SepticElectronics/High-Speed-Timer/PrecisionTimer_RevG.1/IO Plate/IO Plate.png

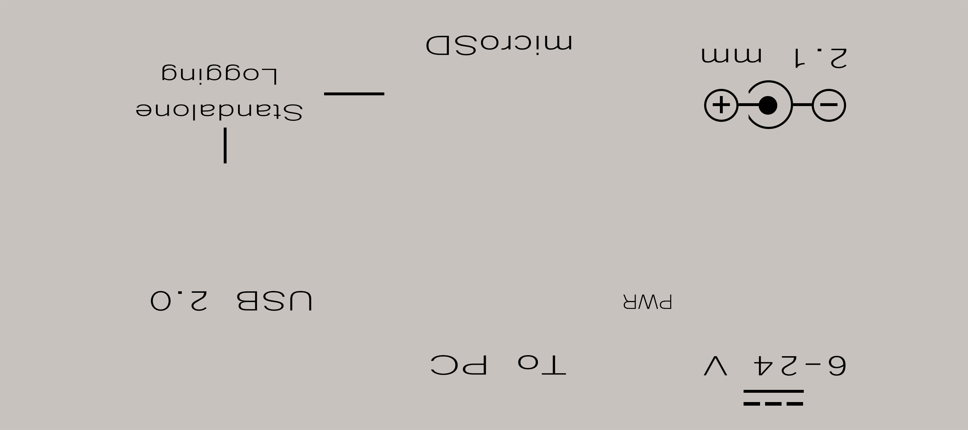
PrecisionTimer_RevG.1/IO Plate/IO Plate.png
