SepticElectronics/High-Speed-Timer/PrecisionTimer_RevG.1/IO Plate/IO Plate_flipped.png

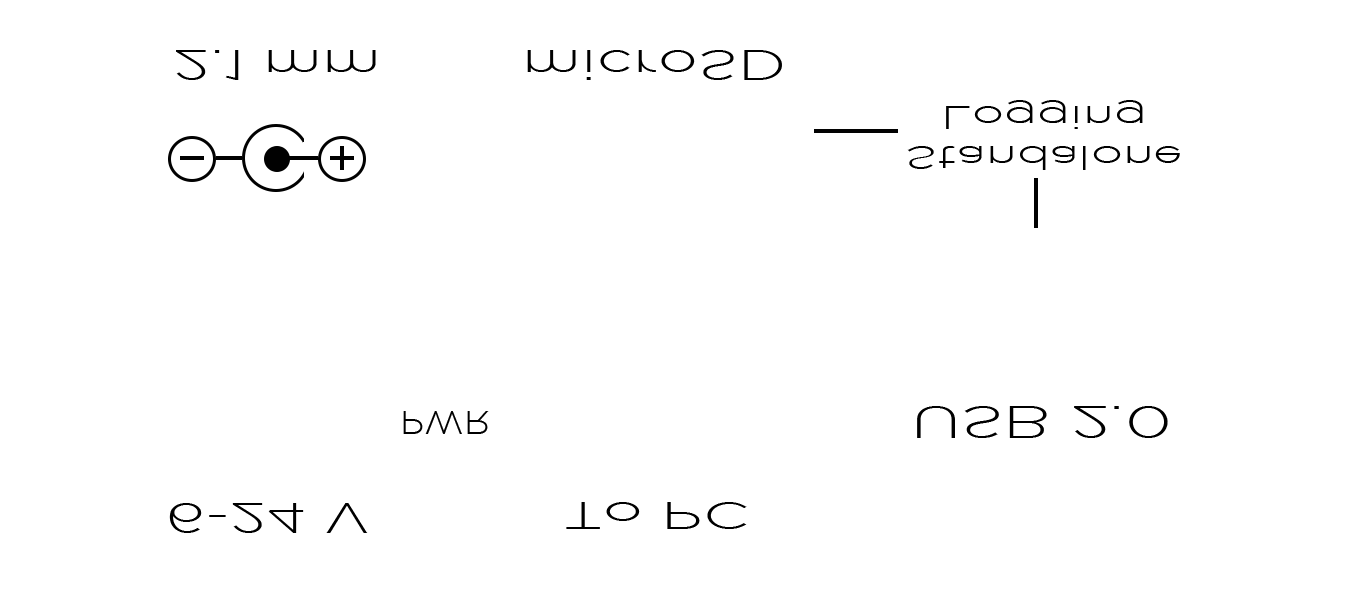
PrecisionTimer_RevG.1/IO Plate/IO Plate_flipped.png
