SepticElectronics/High-Speed-Timer/PrecisionTimer_RevG.1/IO Plate/Trig Plate.png

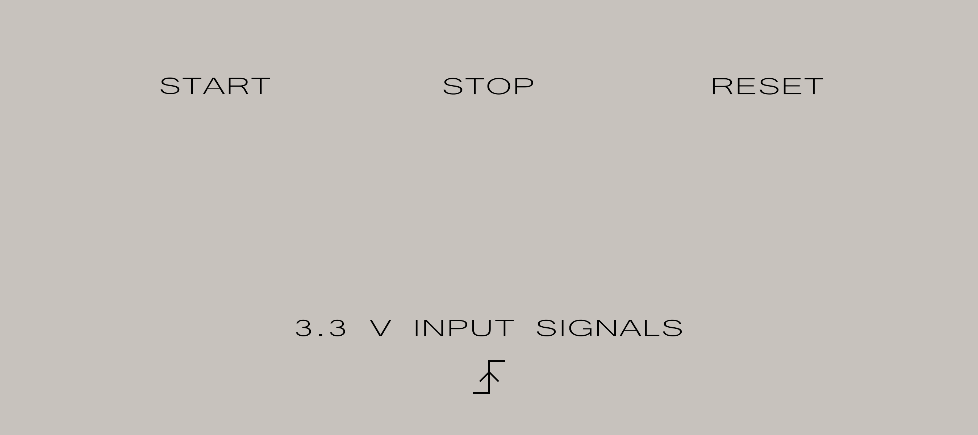
PrecisionTimer_RevG.1/IO Plate/Trig Plate.png
