SepticElectronics/High-Speed-Timer/PrecisionTimer_RevG.1/render/PrecisionTimer_RevG-1_Front2.png

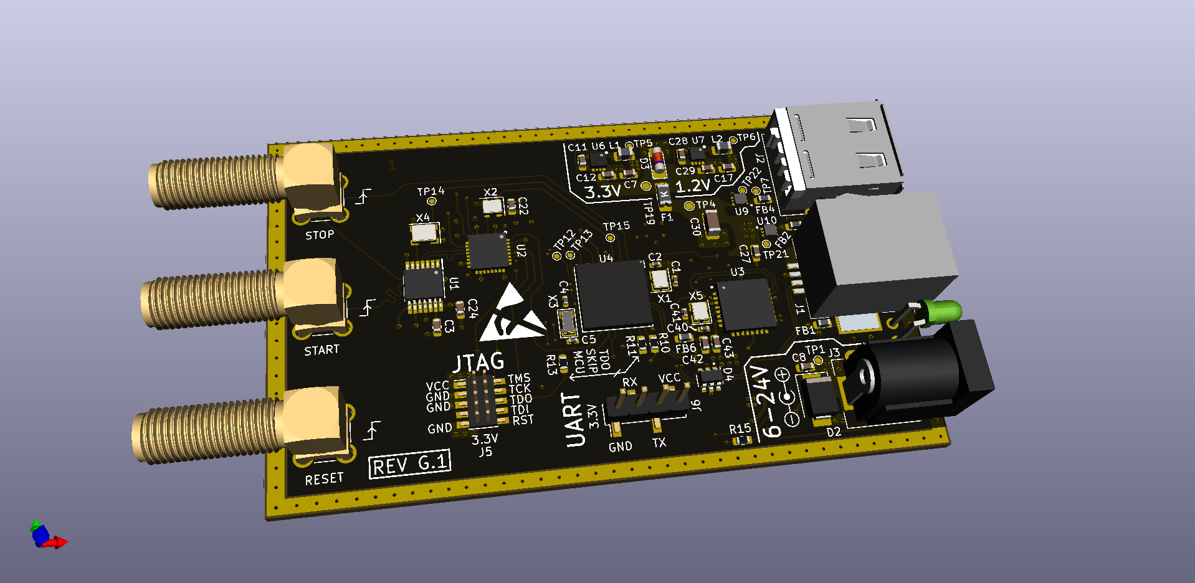
PrecisionTimer_RevG.1/render/PrecisionTimer_RevG-1_Front2.png
