SepticElectronics/High-Speed-Timer/PrecisionTimer_RevG/IO Plate/IO Plate.png

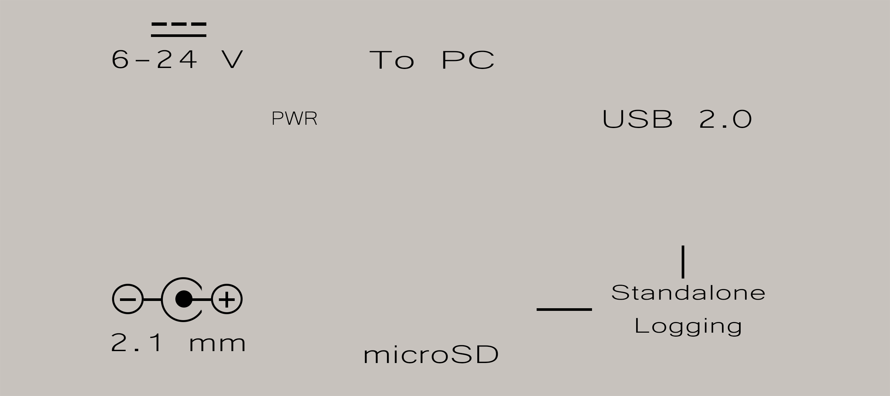
PrecisionTimer_RevG/IO Plate/IO Plate.png
