SepticElectronics/High-Speed-Timer/PrecisionTimer_RevG/render/PrecisionTimer_RevG_F1.png

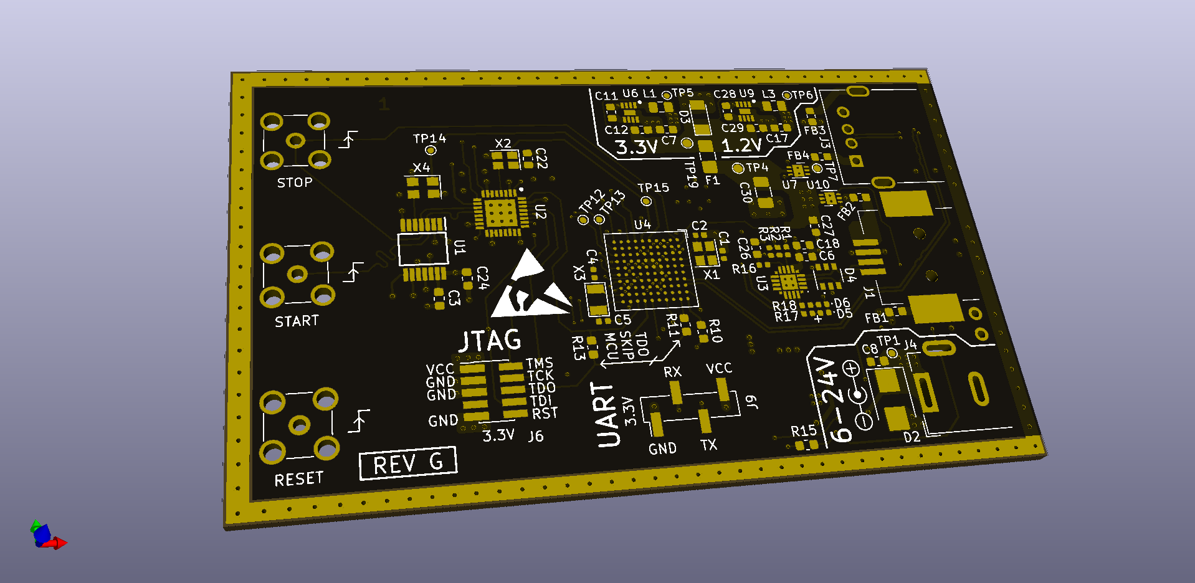
PrecisionTimer_RevG/render/PrecisionTimer_RevG_F1.png
