SepticElectronics/High-Speed-Timer/PrecisionTimer_RevG.1/render/Assembly_2020-Sep-15_06-23-36PM-000_CustomizedView10530445201.png

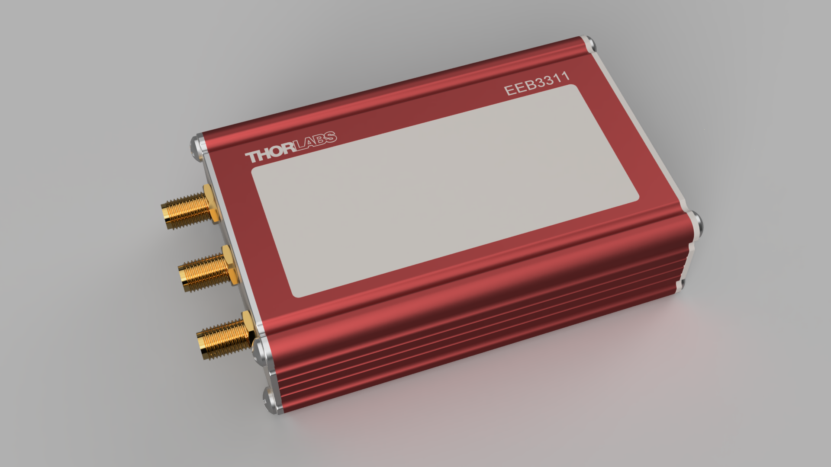
PrecisionTimer_RevG.1/render/Assembly_2020-Sep-15_06-23-36PM-000_CustomizedView10530445201.png
