SepticElectronics/High-Speed-Timer/PrecisionTimer_RevG/render/Assembly_2020-Sep-14_11-25-46PM-000_CustomizedView15014525138.png

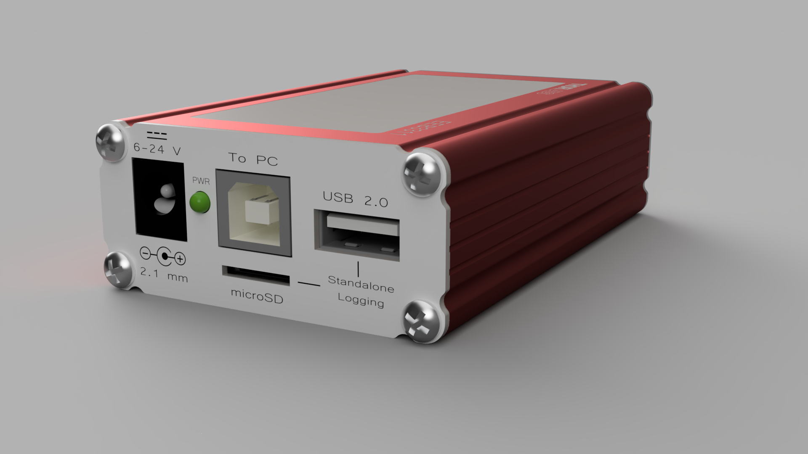
PrecisionTimer_RevG/render/Assembly_2020-Sep-14_11-25-46PM-000_CustomizedView15014525138.png
